ralferoo/cpcfpga/hardware/spice/trans_conv-300mV-alt.asc

Q1: npn
R1: res; 2200
R2: res; 2200
R3: res; 75
R4: res; 680
V1: voltage; 3.3
V2: voltage; SINE(1.65 1.65 1000000)
Named nets: 0
.tran 2us
