ralferoo/cpcfpga/hardware/spice/trans_conv-300mV-pre-npn.asc

Q1: npn
R2: res; 2200
R3: res; 75
R4: res; 1240
V1: voltage; 3.3
V2: voltage; SINE(1.65 1.65 4000000)
V3: voltage; 3.3
Named nets: 0
.tran 2us
want 0.95V before npn to get 0.3v out
