ralferoo/cpcfpga/hardware/spice/trans_conv2bit-700mV-180ohm.asc

Q1: npn
R1: res; 2200
R2: res; 270
R3: res; 75
R4: res; 1000
R5: res; 680
R6: res; 180
R7: res; 4700
V1: voltage; 3.3
V2: voltage; SINE(1.65 1.65 16000000)
V3: voltage; 3.3
Named nets: 0
.tran 2us
V2=3.3, V3=3.3 -> 700.7mV
V2=0, V3=3.3 -> 369.1mV
V2=3.3, V3=0 -> 113.5mV
