ralferoo/cpcfpga/hardware/spice/speaker_volume.asc

C1: cap; 100nF
C2: cap; 100nF
C3: cap; 100nF
R1: res; 1000
R2: res; 2200
R3: res; 75
R6: res; 10000
R7: res; 10000
V1: voltage; SINE(1.65 1.65 10000 0 0 0)
V2: voltage; SINE(1.65 1.65 11000 0 0 0)
Named nets: 0
;tran 0.0005s
.tran 0.0005s
V=IR, 3.3=2275*I, I=1.45mA
http://sim.okawa-denshi.jp/en/CRtool.php gives
lowpass cut-off frequency as 21220
