ralferoo/cpcfpga/hardware/spice/tape.asc

A1: and
C1: cap; 100nF
C2: cap; 4700nF
Q1: npn
Q2: npn
R1: res; 10000
R2: res; 5700
R3: res; 10000
R4: res; 47000
R5: res; 240
R6: res; 2200
R7: res; 4700
R8: res; 270
R9: res; 240
V1: voltage; SINE(0 1 10000 0 0 0)
V2: voltage; 3.3
V3: voltage; PULSE(0 3.3 0 0 0 0.00005 0.0001 1000)
Named nets: 0
.tran 0.0005s
Good info here: http://www.zxdesign.info/cassette.shtml
ds099.pdf p61:
LVTTL/LVCMOS33, V_IL < 0.8V, V_IH > 2.0V
LVCMOS25, V_IL < 0.7V, V_IH > 1.7V
Output, want at least 1.2V swing centred on 1.4V
Before transistor, want 1.2V swing centred on 2.1V
R3=R2/(vin/vout-1)=R2/(3.3/2.1-1)=1.75*R2
R2=R3(vin/vout-1)=R3(1.5714-1)=0.5714*R3
C1 should really be about 4.uF
