ralferoo/cpcfpga/hardware/spice/trans_conv-700mV.asc

Q1: npn
R1: res; 1000
R2: res; 75
R3: res; 75
R4: res; 2200
V1: voltage; 3.3
V2: voltage; SINE(1.65 1.65 1000000)
Named nets: 0
.tran 2us
